apertus-open-source-cinema/beta-hardware/Manufacturing Tools/PCB Reflow Bracket V01/Bracket_TOP_V04.stl

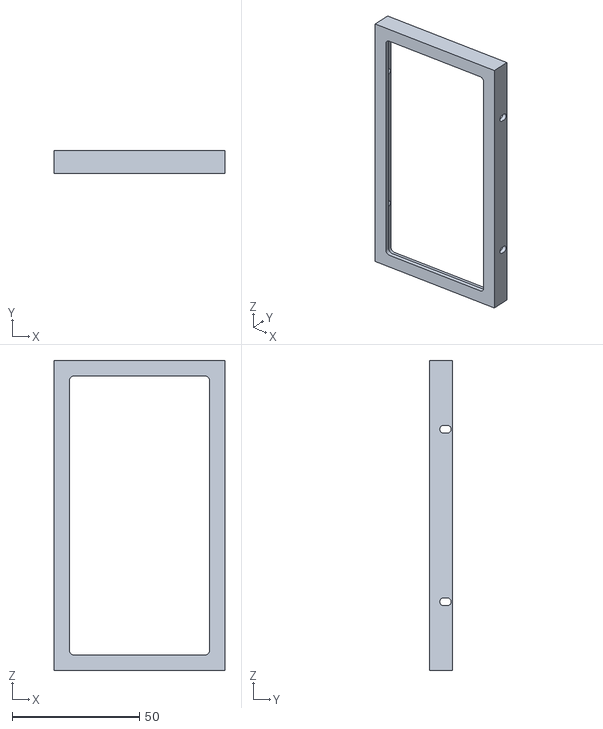
[picture p19: CAD file, 2016-08-06]
Manufacturing Tools/PCB Reflow Bracket V01/Bracket_TOP_V04.stl
67.2 x 9.00 x 121.8
