apertus-open-source-cinema/beta-hardware/Manufacturing Tools/PCB Reflow Hotplate V01/MOSCAM2,5.SLDPRT

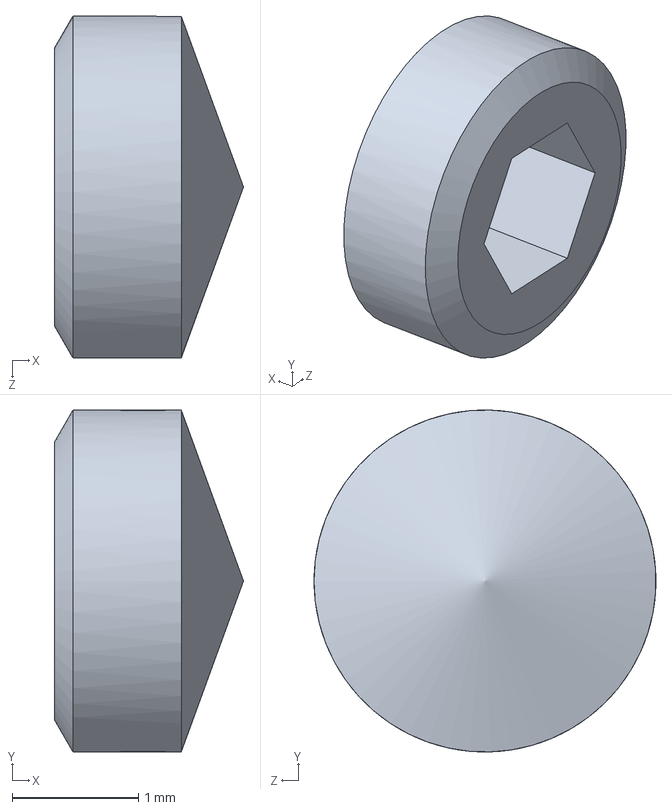
[picture p20: CAD file, 2016-08-11]
Manufacturing Tools/PCB Reflow Hotplate V01/MOSCAM2,5.SLDPRT
1.50 x 2.71 x 2.71 mm
