apertus-open-source-cinema/beta-hardware/Enclosure/3D-Print-Parts/PCB-Separator-Tool-V01.stl

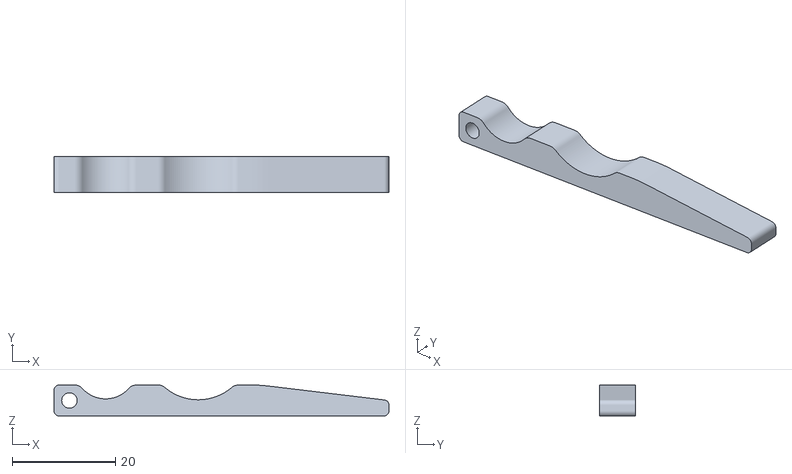
[picture p21: CAD file, 2016-04-12]
Enclosure/3D-Print-Parts/PCB-Separator-Tool-V01.stl
65.0 x 7.00 x 6.00
