apertus-open-source-cinema/beta-hardware/Enclosure/SimpleDesign02/AXIOM LOGO.dxf

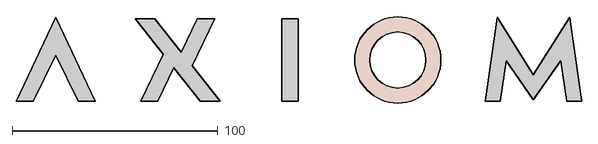
[picture p22: CAD file, 2016-07-31]
Enclosure/SimpleDesign02/AXIOM LOGO.dxf
275.1 x 41.9
