apertus-open-source-cinema/beta-hardware/Enclosure/Skeleton_E-mount/Sensormount_CMV12000_H.stl

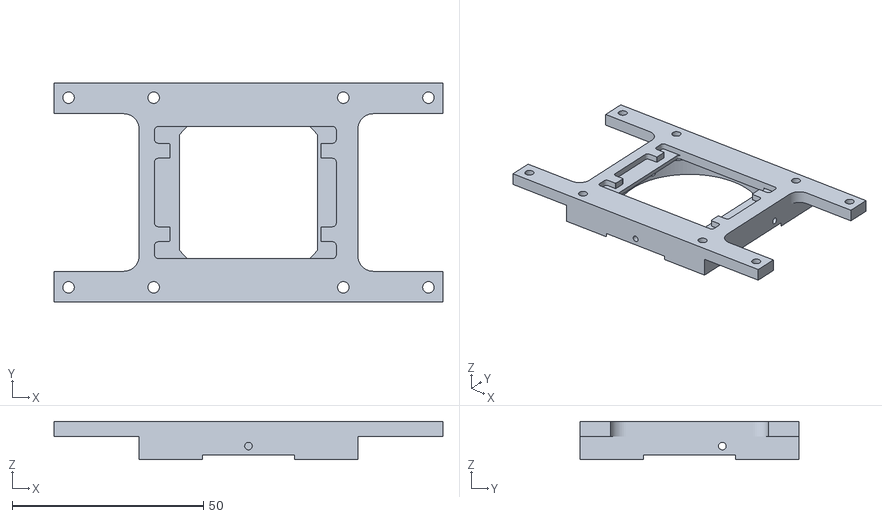
[picture p23: CAD file, 2015-04-28]
Enclosure/Skeleton_E-mount/Sensormount_CMV12000_H.stl
101.6 x 57.2 x 10.0
