apertus-open-source-cinema/beta-hardware/Enclosure/SkeletonV03/Skeleton V03fix-microzed-cut.stl

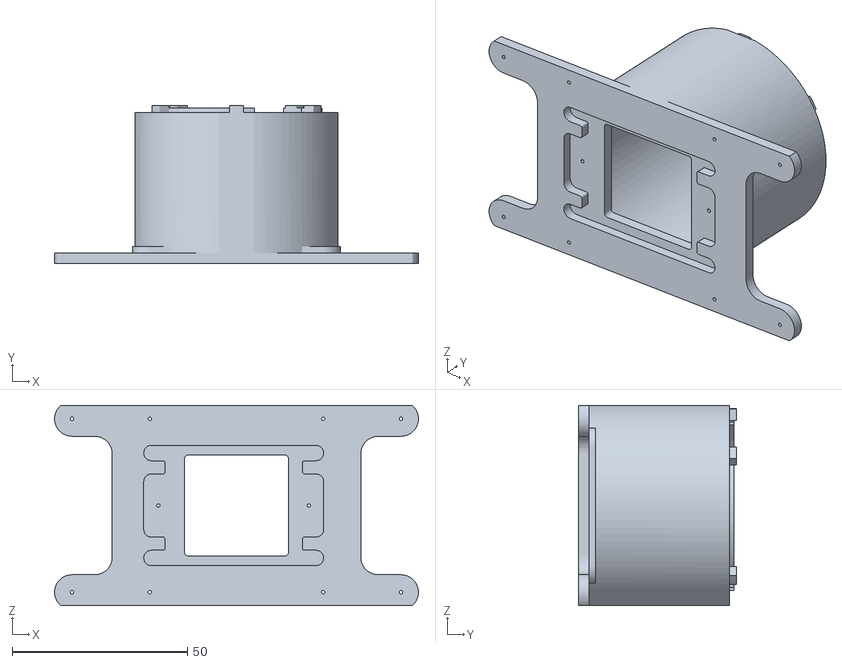
[picture p24: CAD file, 2015-04-03]
Enclosure/SkeletonV03/Skeleton V03fix-microzed-cut.stl
104.0 x 45.0 x 57.2
