apertus-open-source-cinema/beta-hardware/Enclosure/Version 002/BetaSkeletonV01.stp

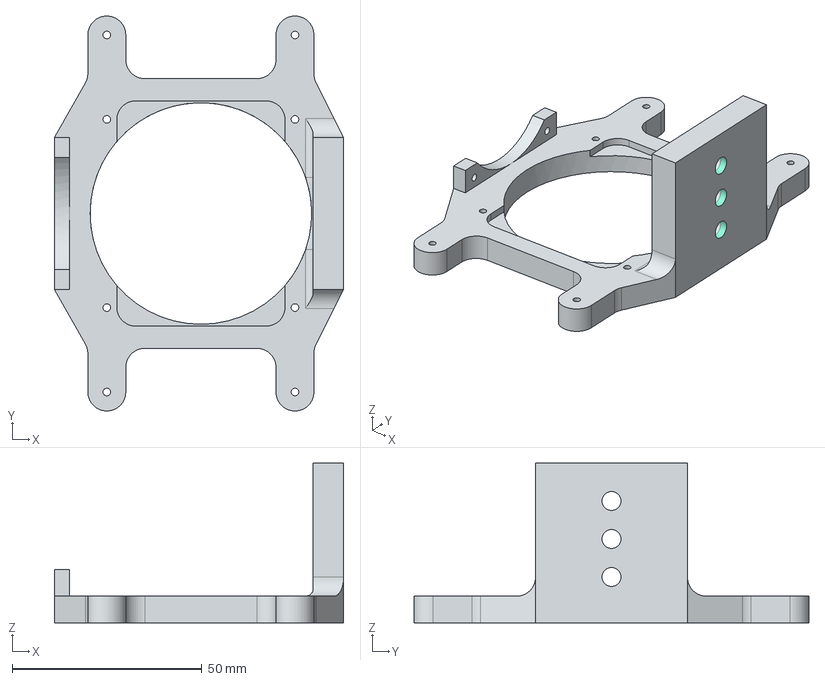
[picture p25: CAD file, 2015-03-13]
Enclosure/Version 002/BetaSkeletonV01.stp
76.2 x 104.0 x 42.0 mm
