apertus-open-source-cinema/beta-hardware/Manufacturing Tools/CMV12000 Extraction Tool V01/3d print/arms02.stl

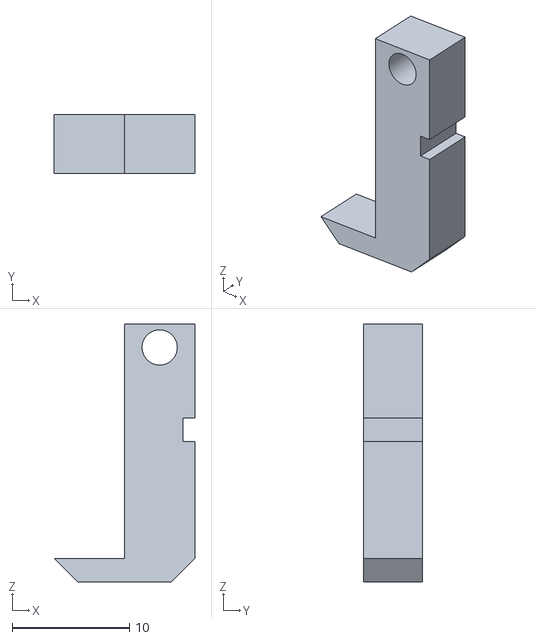
[picture p26: CAD file, 2016-10-09]
Manufacturing Tools/CMV12000 Extraction Tool V01/3d print/arms02.stl
12.0 x 5.00 x 22.0
