apertus-open-source-cinema/beta-hardware/Manufacturing Tools/PCB Reflow Hotplate V01/KFL08.STEP

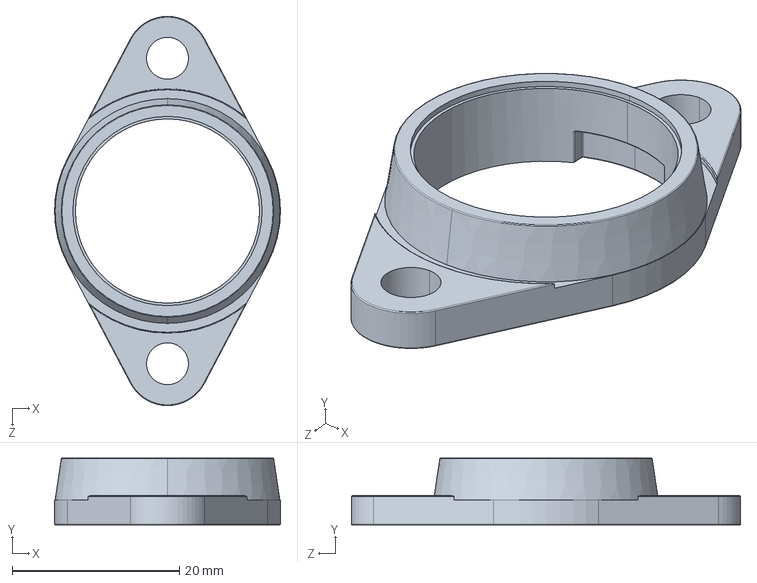
[picture p27: CAD file, 2016-08-11]
Manufacturing Tools/PCB Reflow Hotplate V01/KFL08.STEP
27.0 x 8.00 x 46.5 mm
