apertus-open-source-cinema/beta-hardware/Enclosure/3D-Print-Parts/Skeleton-Emount.stl

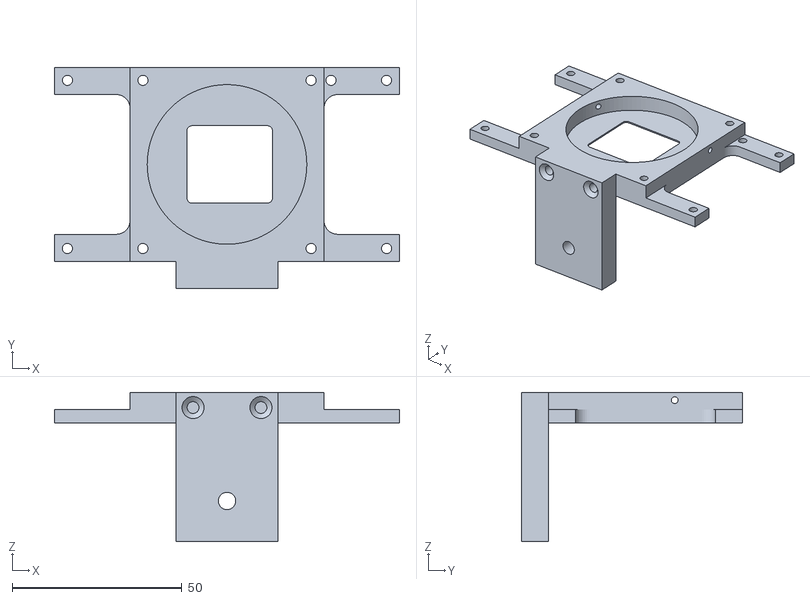
[picture p28: CAD file, 2016-02-12]
Enclosure/3D-Print-Parts/Skeleton-Emount.stl
101.6 x 65.2 x 44.0
