apertus-open-source-cinema/beta-hardware/Enclosure/SimpleDesign02/Simple3DPrintEnclosure01.stp

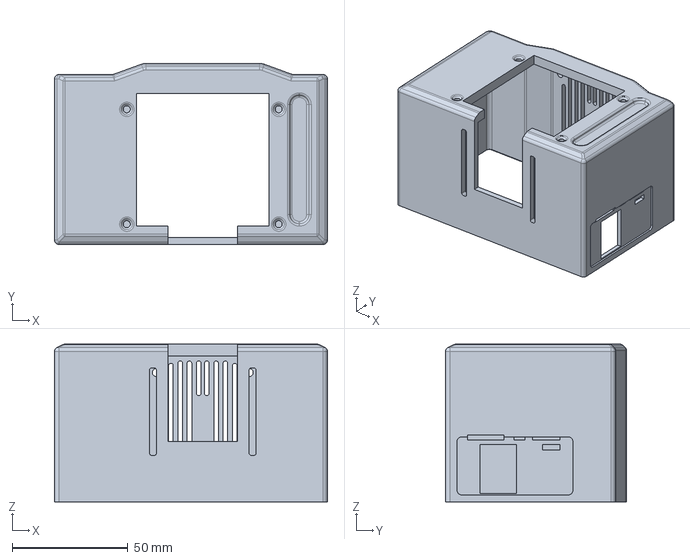
[picture p29: CAD file, 2016-07-31]
Enclosure/SimpleDesign02/Simple3DPrintEnclosure01.stp
117.8 x 78.2 x 68.0 mm
