apertus-open-source-cinema/beta-hardware/Enclosure/Skeleton_E-mount/Sensormount_CMV12000_XL.stl

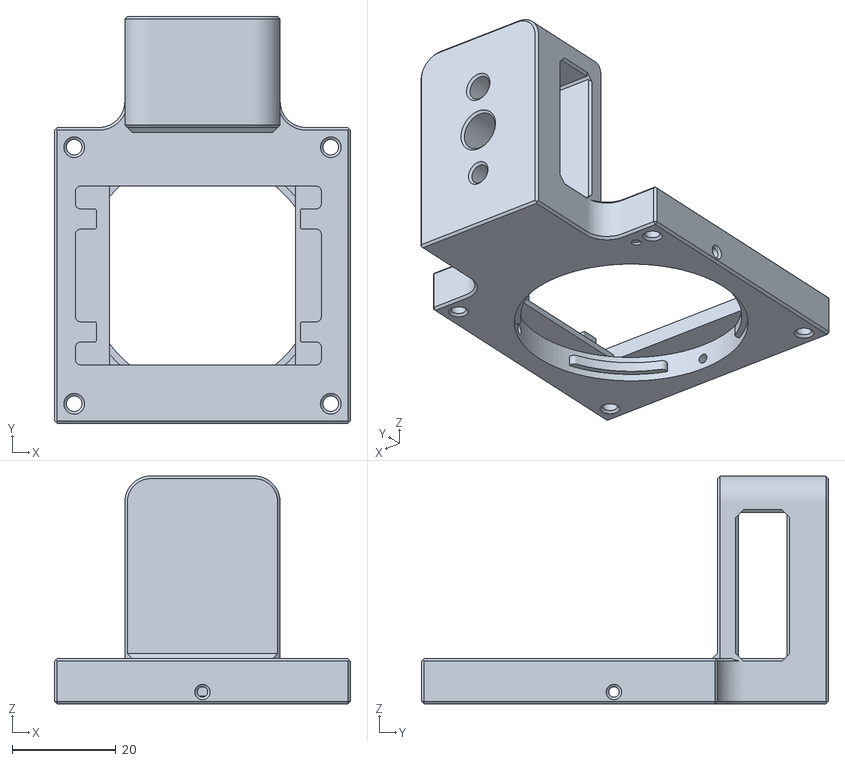
[picture p30: CAD file, 2015-04-04]
Enclosure/Skeleton_E-mount/Sensormount_CMV12000_XL.stl
57.2 x 78.6 x 44.0
