apertus-open-source-cinema/beta-hardware/Enclosure/Version 002/User Library-Mini Displayport Molex-sd-105081-001.STEP

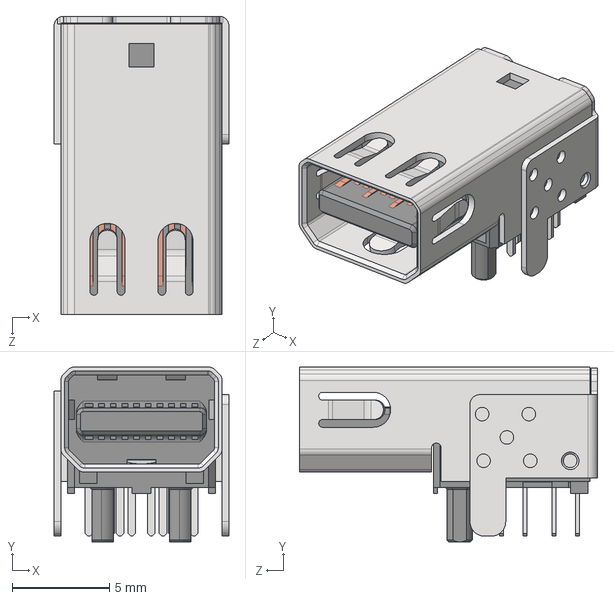
[picture p31: CAD file, 2015-02-22]
Enclosure/Version 002/User Library-Mini Displayport Molex-sd-105081-001.STEP
9.00 x 9.00 x 15.4 mm
