apertus-open-source-cinema/beta-hardware/Manufacturing Tools/CMV12000 Extraction Tool V01/3d print/Knob.stl

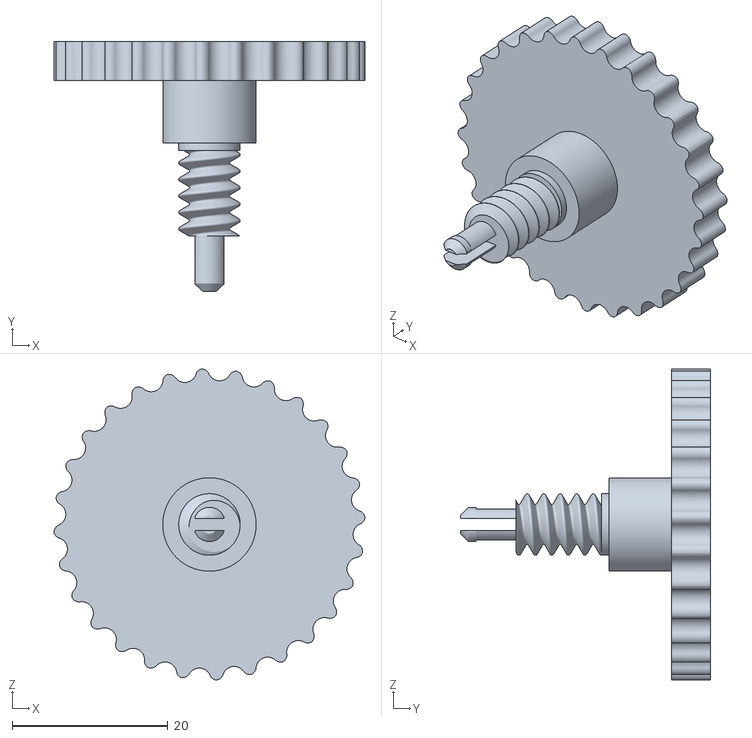
[picture p32: CAD file, 2016-09-18]
Manufacturing Tools/CMV12000 Extraction Tool V01/3d print/Knob.stl
40.0 x 32.1 x 40.0
