apertus-open-source-cinema/beta-hardware/Manufacturing Tools/PCB Reflow Hotplate V01/608RS.SLDPRT

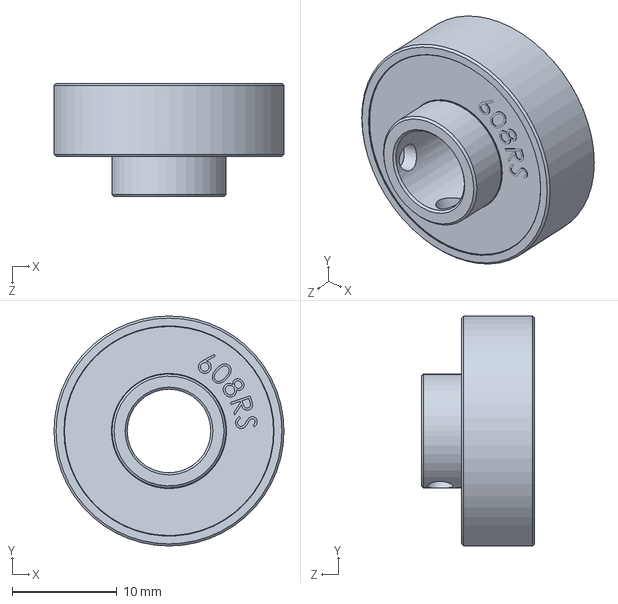
[picture p33: CAD file, 2016-08-11]
Manufacturing Tools/PCB Reflow Hotplate V01/608RS.SLDPRT
22.0 x 22.0 x 10.9 mm
