apertus-open-source-cinema/beta-hardware/Enclosure/3D-Print-Parts/SimpleDesignV2-R02-Front.stl

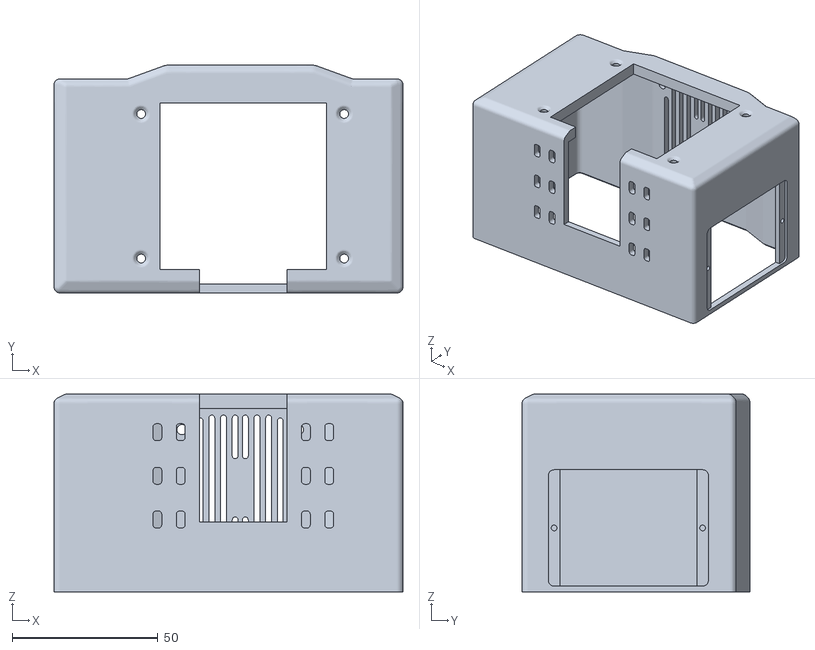
[picture p34: CAD file, 2016-02-12]
Enclosure/3D-Print-Parts/SimpleDesignV2-R02-Front.stl
119.9 x 78.2 x 68.0
