apertus-open-source-cinema/beta-hardware/Enclosure/Skeleton_E-mount/Sensormount_CMV12000_L.stl

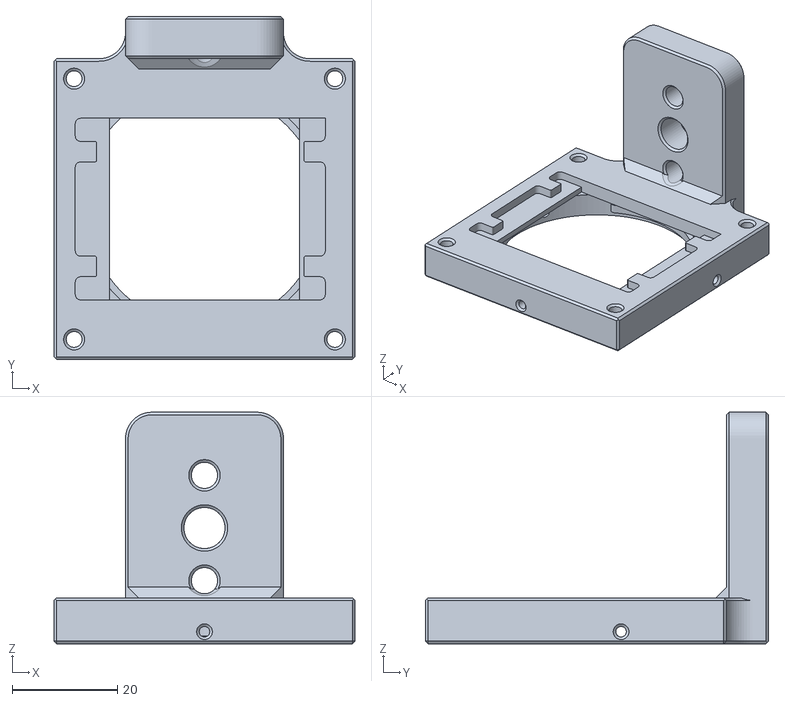
[picture p35: CAD file, 2015-04-04]
Enclosure/Skeleton_E-mount/Sensormount_CMV12000_L.stl
57.2 x 65.2 x 44.0
