apertus-open-source-cinema/beta-hardware/Enclosure/SkeletonV03/Skeleton V03.stp

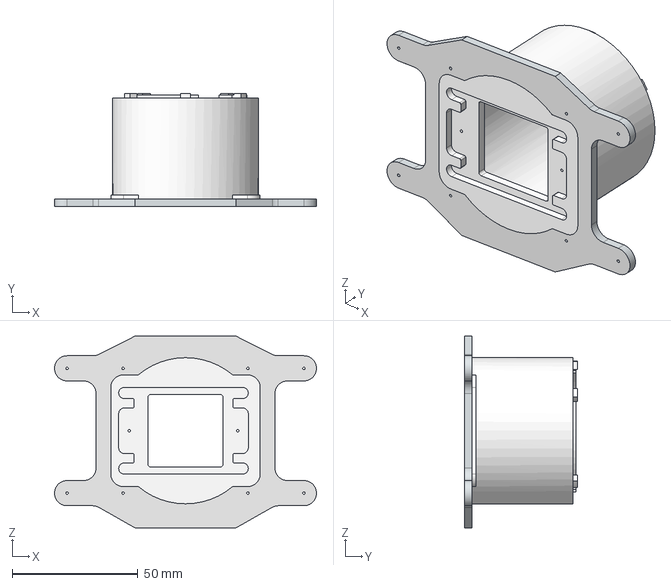
[picture p36: CAD file, 2015-04-02]
Enclosure/SkeletonV03/Skeleton V03.stp
104.0 x 45.0 x 76.2 mm
