apertus-open-source-cinema/beta-hardware/Manufacturing Tools/CMV12000 Extraction Tool V01/3d print/mover.stl

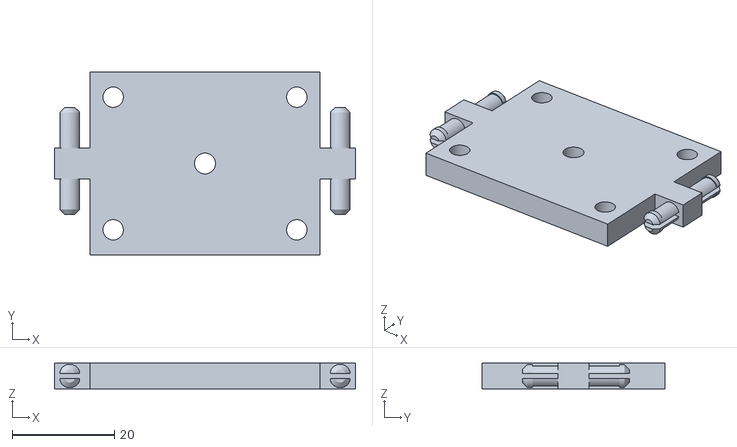
[picture p37: CAD file, 2016-09-18]
Manufacturing Tools/CMV12000 Extraction Tool V01/3d print/mover.stl
59.0 x 35.9 x 5.00
