apertus-open-source-cinema/beta-hardware/Enclosure/3D-Print-Parts/SimpleDesignV2-R02-Back.stl

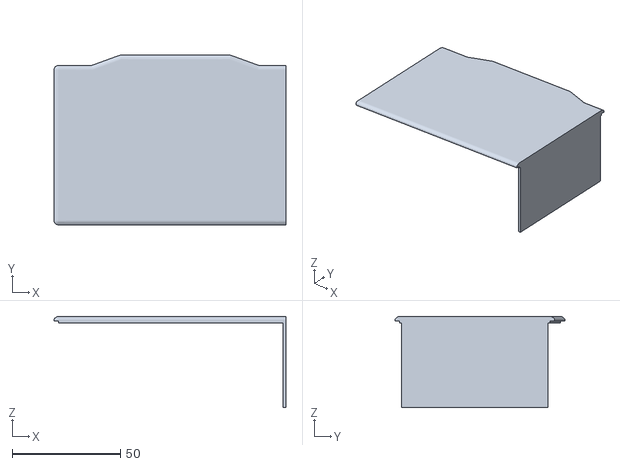
[picture p38: CAD file, 2016-02-12]
Enclosure/3D-Print-Parts/SimpleDesignV2-R02-Back.stl
107.0 x 78.2 x 42.0
