apertus-open-source-cinema/beta-hardware/Manufacturing Tools/CMV12000 Extraction Tool V01/3d print/base.stl

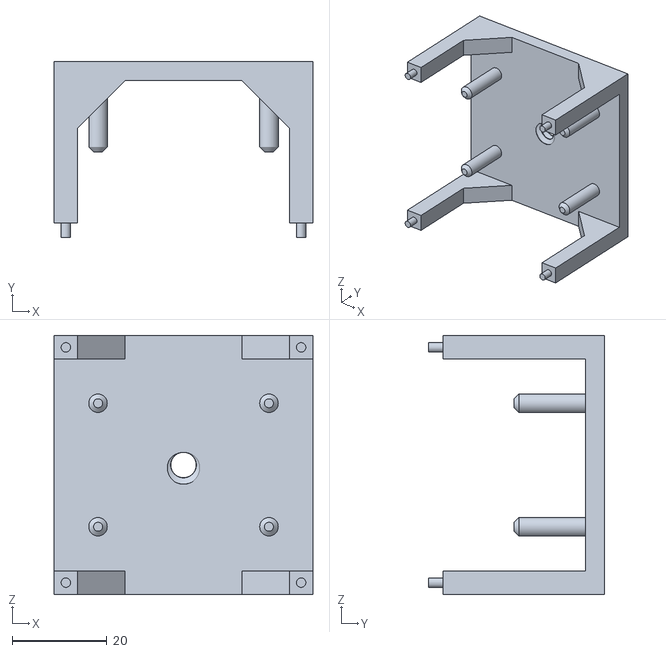
[picture p39: CAD file, 2016-09-18]
Manufacturing Tools/CMV12000 Extraction Tool V01/3d print/base.stl
54.5 x 37.0 x 54.5
