apertus-open-source-cinema/beta-hardware/Manufacturing Tools/CMV12000 Extraction Tool V01/3d print/arm.stl

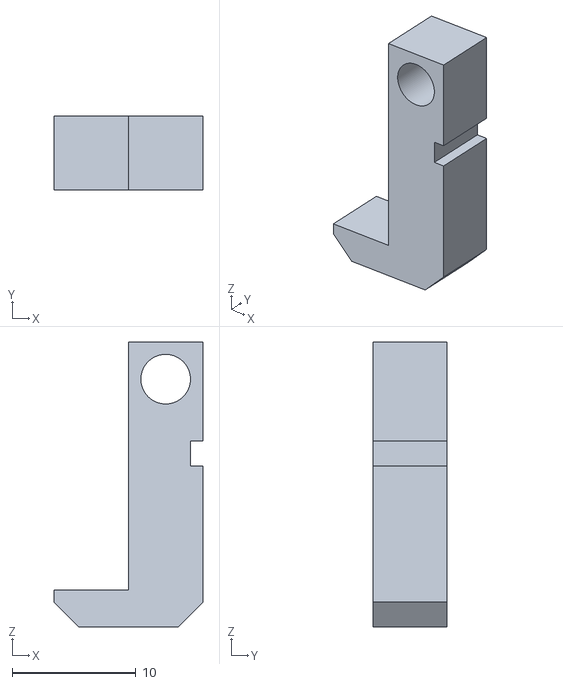
[picture p40: CAD file, 2016-09-18]
Manufacturing Tools/CMV12000 Extraction Tool V01/3d print/arm.stl
12.0 x 6.00 x 23.0
