apertus-open-source-cinema/beta-hardware/Enclosure/3D-Print-Parts/HDMIPluginModuleHolder02.stl

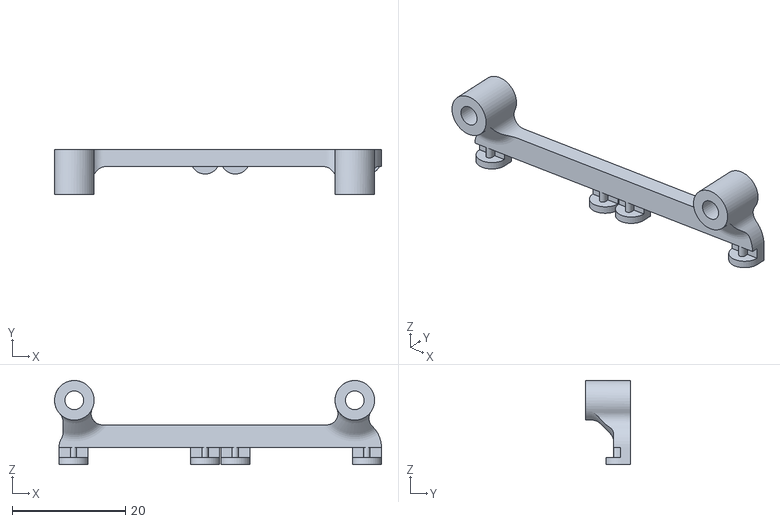
[picture p41: CAD file, 2015-10-30]
Enclosure/3D-Print-Parts/HDMIPluginModuleHolder02.stl
57.7 x 8.00 x 14.8
