apertus-open-source-cinema/beta-hardware/Enclosure/3D-Print-Parts/HDMIPluginModuleHolder01.stl

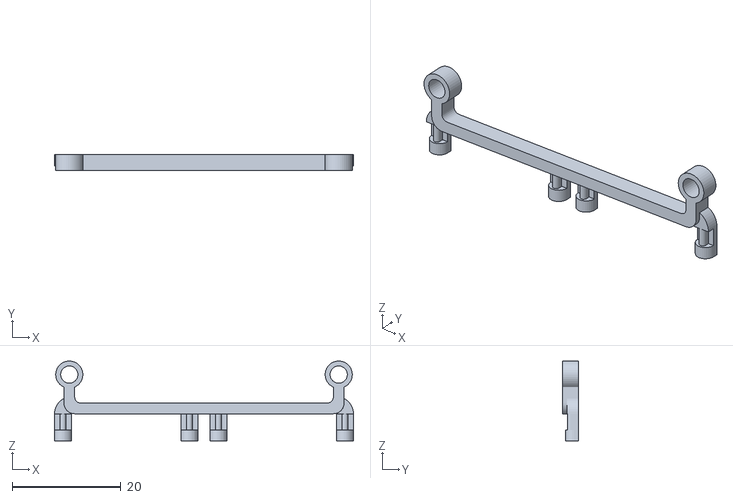
[picture p42: CAD file, 2015-10-15]
Enclosure/3D-Print-Parts/HDMIPluginModuleHolder01.stl
55.0 x 3.00 x 14.7
